jbilander/Gotek_internal_A500_mount/images/Gotek_internal_a500_mounting_bracket_i2c_usb_pic19.jpg

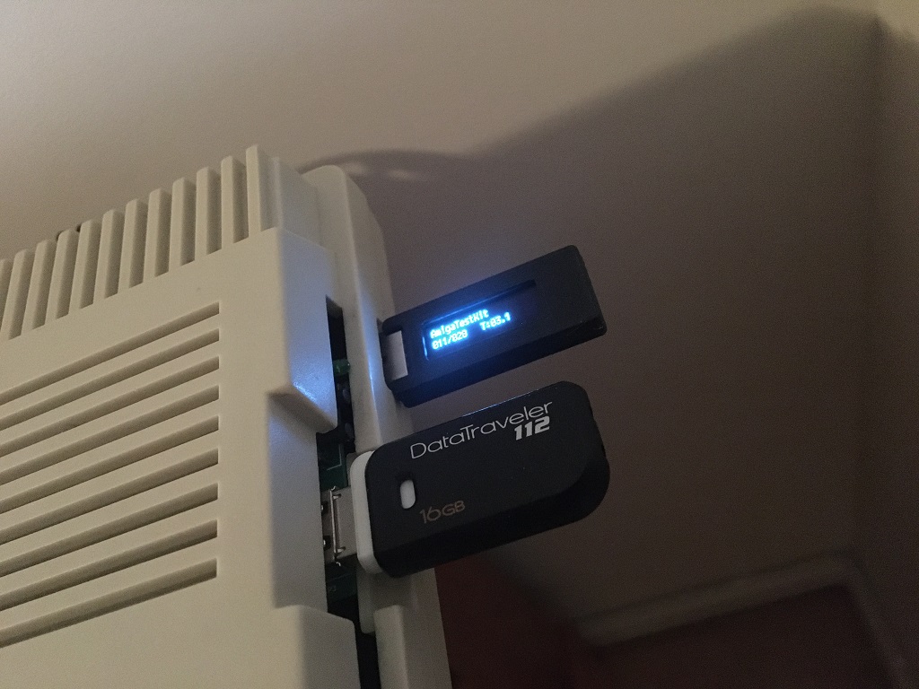
images/Gotek_internal_a500_mounting_bracket_i2c_usb_pic19.jpg
