jbilander/Gotek_internal_A500_mount/images/Gotek_internal_a500_mounting_bracket_usb.jpg

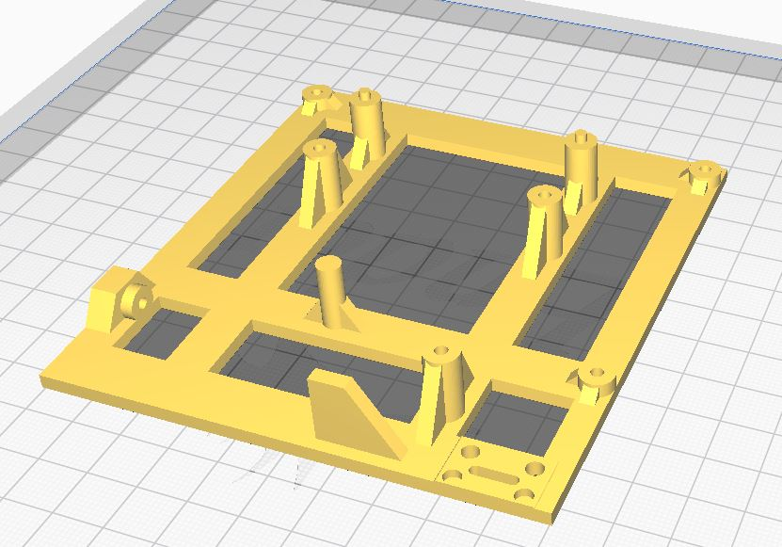
images/Gotek_internal_a500_mounting_bracket_usb.jpg
